IDEA-1-61/6signalDataLogger/Imagenes/photo_2023-06-01_10-36-32.jpg

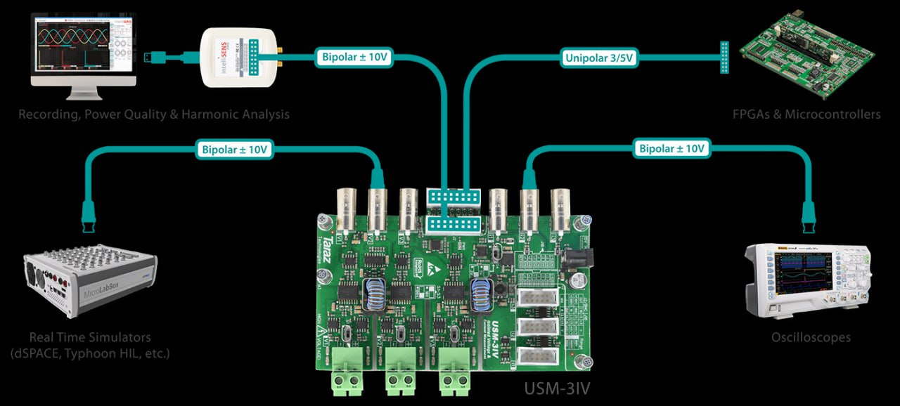
Imagenes/photo_2023-06-01_10-36-32.jpg
