IDEA-1-61/6signalDataLogger/Imagenes/photo_2023-06-17_18-40-50.jpg

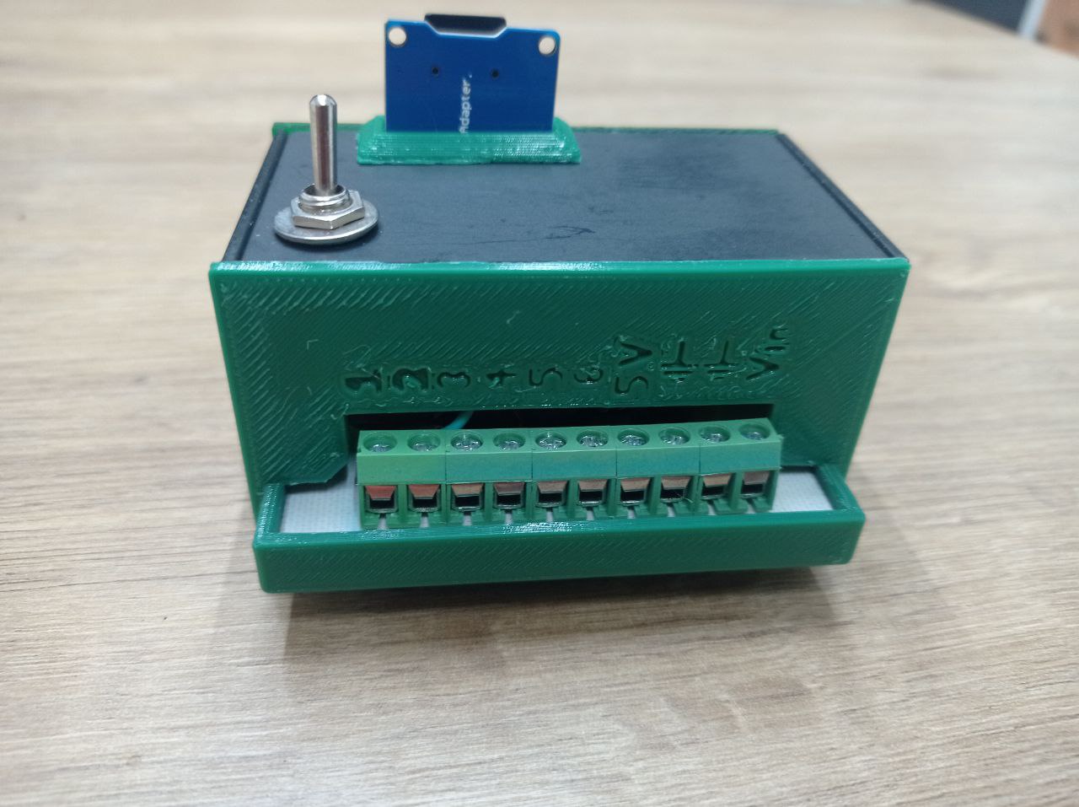
Imagenes/photo_2023-06-17_18-40-50.jpg
