IDEA-1-61/6signalDataLogger/Imagenes/photo_2023-06-17_18-41-13.jpg

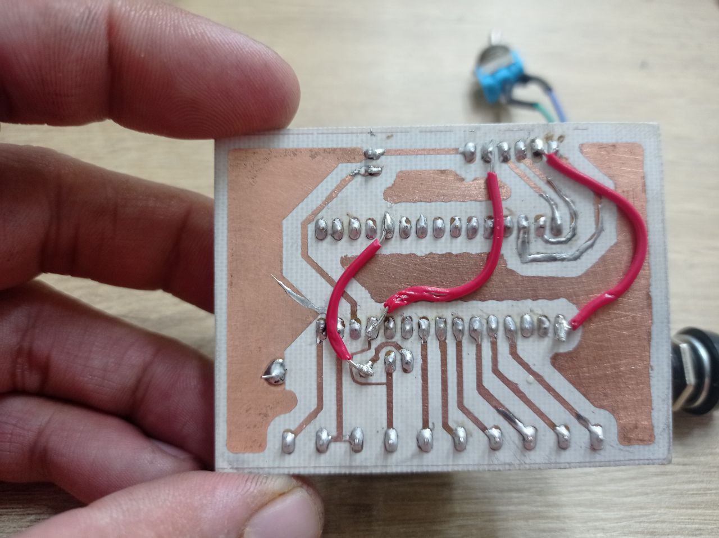
Imagenes/photo_2023-06-17_18-41-13.jpg
