IDEA-1-61/6signalDataLogger/Imagenes/photo_2023-06-17_18-42-01.jpg

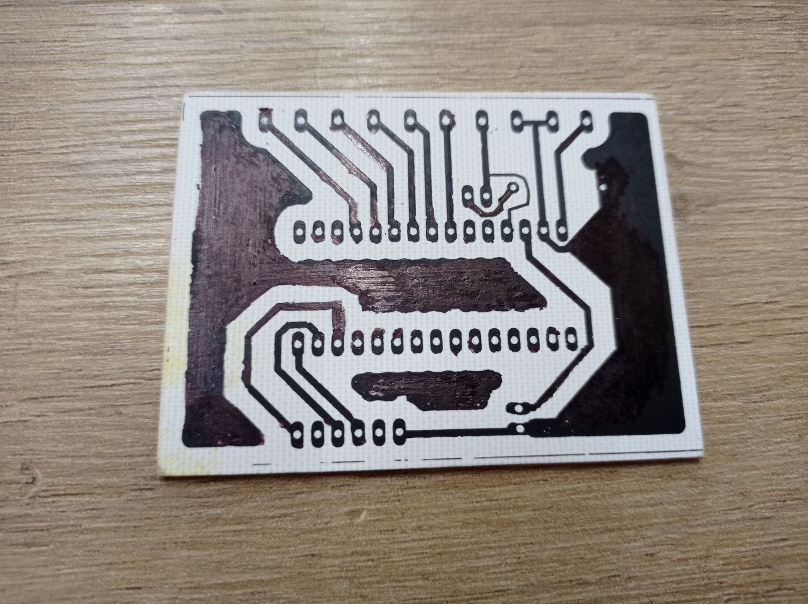
Imagenes/photo_2023-06-17_18-42-01.jpg
